yu2924/XPS/enclosure/3dprints/FrontPanelSpacerPlane.dxf

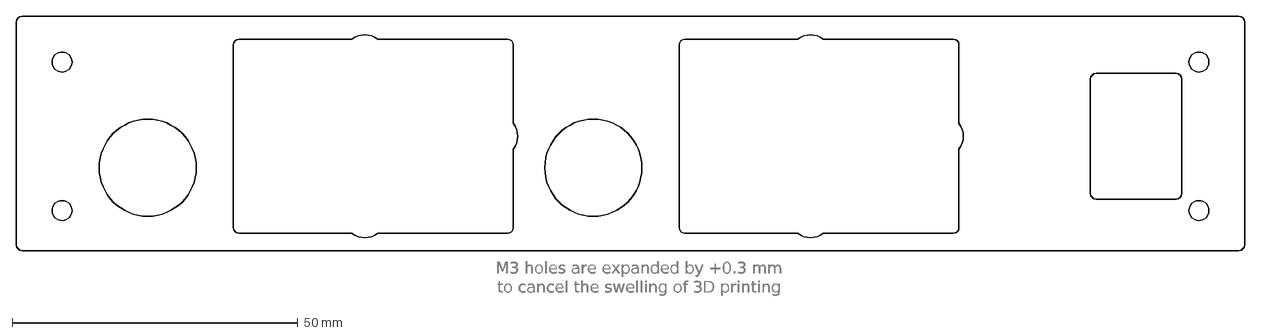
[picture p30: CAD file, 2022-06-04]
enclosure/3dprints/FrontPanelSpacerPlane.dxf
M3 holes are expanded by +0.3 mm to cancel the swelling of 3D printing
