yu2924/XPS/sim/LineDriver-ac.asc

C1: cap; {CL}
C2: cap; 22µ
C3: cap; 22µ
C4: cap; {CL}
C5: cap; {CC}
C6: cap; {CC}
C7: cap; {CC}
C8: cap; {CC}
R1: res; 20k
R2: res; 10k
R3: res; 20k
R4: res; 10k
R5: res; 51
R6: res; 20k
R7: res; 20k
R8: res; 10k
R9: res; 10k
R10: res; 51
R11: res; 10k
R12: res; 10k
R13: res; 10k
R14: res; 10k
U1: opamp2; OPA1602
U2: opamp2; OPA1602
U3: opamp2; OPA1602
V1: voltage; SINE(0 1 1k); AC 1
V2: voltage; 11
V3: voltage; 11
Named nets: 0, hot, cold, bias, vcc
.ac dec 10 10 20Meg
.param CC=10p CL=100p
.lib TI/OPA1602.lib
