yu2924/XPS/sim/LineDriver-sensitivity.asc

C1: cap; 22µ
C4: cap; 22µ
C5: cap; {CL}
C6: cap; {CL}
C7: cap; {CC}
C8: cap; {CC}
C9: cap; {CC}
C10: cap; {CC}
R15: res; {mc(20k,tol)}
R16: res; {mc(10k,tol)}
R17: res; {mc(20k,tol)}
R18: res; {mc(10k,tol)}
R19: res; 51
R20: res; {mc(20k,tol)}
R21: res; {mc(20k,tol)}
R22: res; {mc(10k,tol)}
R23: res; {mc(10k,tol)}
R24: res; 51
R25: res; 10k
R26: res; 10k
R27: res; 10k
R28: res; 10k
U4: opamp2; OPA1602
U5: opamp2; OPA1602
U6: opamp2; OPA1602
V4: voltage; SINE(0 1 1k); AC 1
V5: voltage; 11
V6: voltage; 11
Named nets: 0, hot, cold, bias, vcc
.tran 10m
.param CC=10p CL=100p
.lib TI/OPA1602.lib
.param tol=0.001
.step param i 0 9 1
