yu2924/XPS/sim/PowerLossEstimation.asc

C1: cap; 47µ
C2: cap; 3300µ; Rser=0.1
C3: cap; 3300µ; Rser=0.1
C4: cap; 47µ
D2: schottky; 1N5819
D3: schottky; 1N5819
D4: schottky; 1N5819
D5: schottky; 1N5819
L1: ind2; 1
L2: ind2; 1
L3: ind2; 1
Load: bi; I=max(0, -0.03+0.3*time)
R1: res; 10k
R2: res; 1.25k
R3: res; 10k
R4: res; 1.25k
R5: res; 2.04
R6: res; 2.04
R7: res; 2.04
U1: LT1963A
U2: LT3015
V4: voltage; SINE(0 21.5625 50)
Named nets: outh, outl, 0, inh, inl
.tran 1.1
K L1 L2 L3 1
100VAC: Vs=18.75
115VAC: Vs=21.5625
